Incomprehensible/Mad_PlantBug/pictures/trace_bcu.png

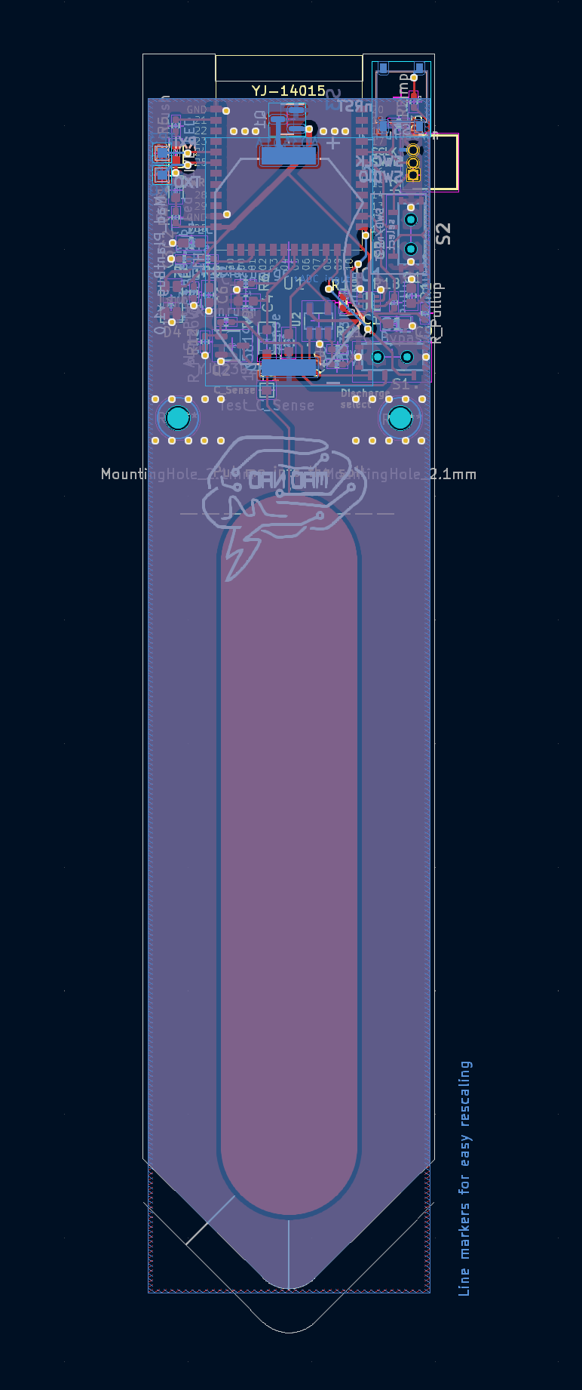
pictures/trace_bcu.png
